akoen/SPICE-Y/pcbs/3D Models/Resistor TH vertical 2,54.stp

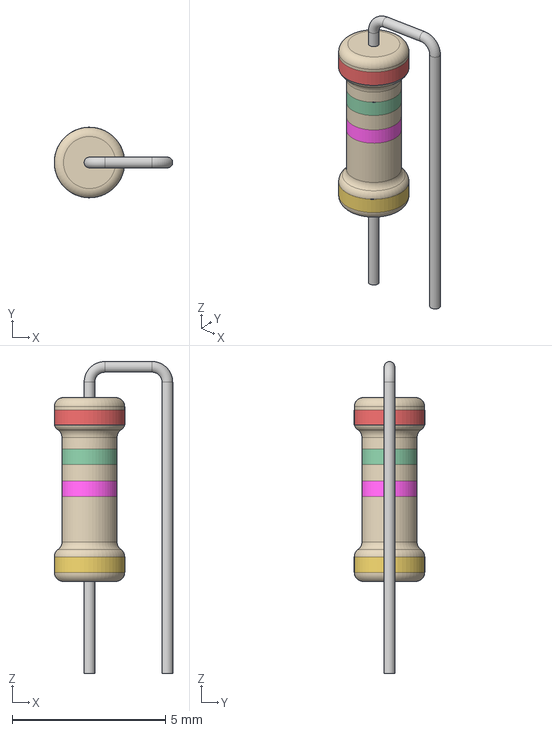
[picture p16: CAD file, 2022-08-12]
pcbs/3D Models/Resistor TH vertical 2,54.stp
3.86 x 2.30 x 10.2 mm
