akoen/SPICE-Y/pcbs/3D Models/3352T-1-502LF.STEP

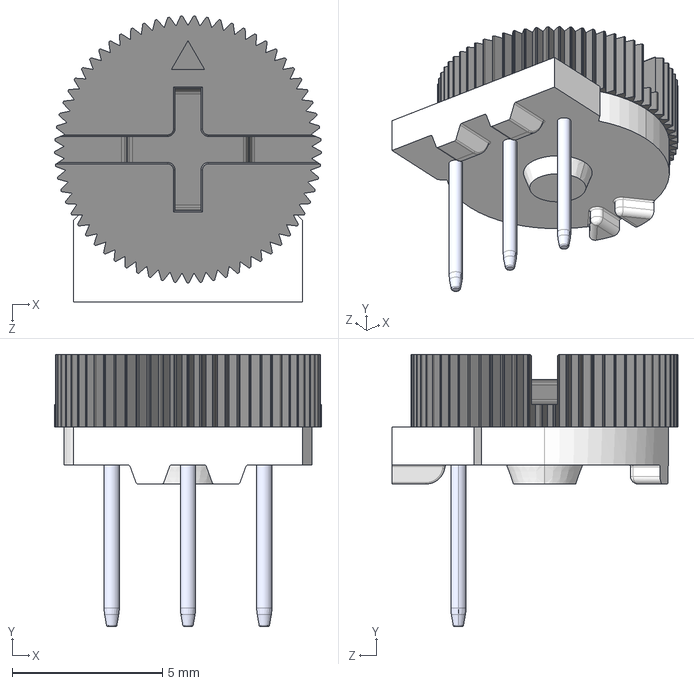
[picture p17: CAD file, 2022-08-12]
pcbs/3D Models/3352T-1-502LF.STEP
8.89 x 9.07 x 9.52 mm
