akoen/SPICE-Y/pcbs/3D Models/3290W001.stp

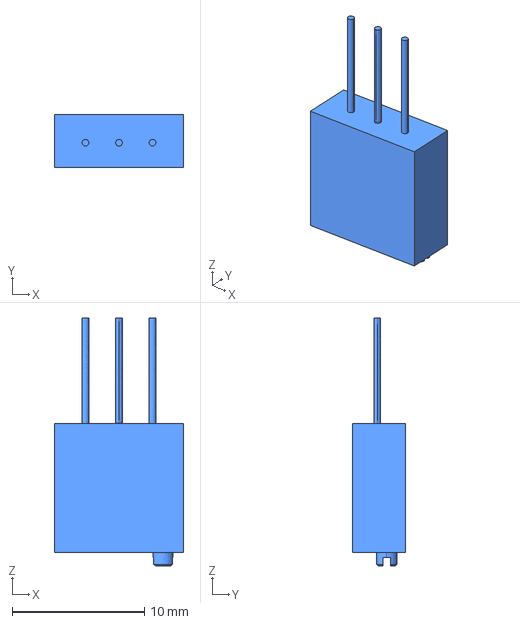
[picture p18: CAD file, 2022-08-12]
pcbs/3D Models/3290W001.stp
9.78 x 4.01 x 18.8 mm
