akoen/SPICE-Y/sims/IR Bandpass Filters.asc

C1: cap; 2n
C2: cap; 1n
C3: cap; 2n
C4: cap; 1n
C5: cap; 2n
C6: cap; 1n
C7: cap; 10n
R1: res; 20k
R2: res; 10k
R3: res; 10k
R4: res; 20k
R5: res; 10k
R6: res; 20k
R7: res; 30k
U1: UniversalOpAmp
U2: UniversalOpAmp
V1: voltage; 7
V2: voltage; 7
Vin1: voltage; ""; AC 1
Vin2: voltage; ""; AC 1
Vin: voltage; ""; AC 1
Named nets: 0, High-pass, Output
f = 1/(2piRC)
.ac lin 1000 1 50k
.param t_on=0.5*{period}
.param period=1/{frequency}
.param frequency=1000
