akoen/SPICE-Y/test/servo-example.cpp

// #include <Arduino.h>
// #include <Servo.h>

// int armServoPin = PB6;
// #define ARM_PWM_FORMAT PB_6
// Servo clawServo;
// Servo armServo;

// void setup() {
// //   armServo.attach(armServoPin);
// }

// void loop() {
//   //close claw
// //   clawServo.write(50);
// //   delay(1000);

//   //lift arm
// //   armServo.write(115);
// //   delay(1000);

//   //open Claw
// //   clawServo.write(100);
// //   delay(1000);
// //   clawServo.write(180);

//   //lower Arm
// //   armServo.write(0);
// //   delay(1000);
// }
